jc2409/SF4_Data_Logger/schematics/LTSpice/audio_output_stage.asc

B1: bv; V=if(V(AUDIO) > V(TIMER), 5, 0)
C1: cap; 15n
C2: cap; 15n
C3: cap; 10u
R1: res; 2.2k
R2: res; 2.2k
R3: res; 220
U1: opamp2; LMX58_LM2904
U2: opamp2; LMX58_LM2904
V1: voltage; 5
V2: voltage; SINE(1.5 1.0 400)
V3: voltage; PULSE(0 5 0 8u 8u 1p 16u)
Named nets: 0, AUDIO, TIMER
.tran 50m
.lib snom268c/lmx58_lm2904.lib
.ic V(n003)=2.5 V(n002)=2.5
