jc2409/SF4_Data_Logger/schematics/LTSpice/full_circuit.asc

C1: cap; 10µ
C2: cap; 10µ
C3: cap; 10µ
C4: cap; 2.2n
C5: cap; 2.2n
C6: cap; 4.7µ
R1: res; 10k
R2: res; 10k
R3: res; 1Meg
R4: res; 10k
R5: res; 100k
R6: res; {R_LDR}
R7: res; 10k
R8: res; 10k
R9: res; 15k
R10: res; 15k
R11: res; 1Meg
U1: opamp2; TL072
U2: LTC6078
U3: opamp2; TL072
U4: LTC6078
U5: opamp2; LMX58_LM2904
V1: voltage; 5
V2: voltage; SINE(0 0.1 400); AC 1
Named nets: 0
.tran 10m
.inc sloj067/TL072.301
.step param R_LDR 100 100k 20k
.lib snom268c/lmx58_lm2904.lib
