jc2409/SF4_Data_Logger/schematics/LTSpice/output_stage.asc

B1: bv; V=if(V(AUDIO) > V(TIMER), 5, 0)
C1: cap; 33n
C2: cap; 10µ
R1: res; 1k
R2: res; 100k
U1: opamp2; LMX58_LM2904
V1: voltage; 5
V2: voltage; SINE(1.75 1.5 400)
V3: voltage; PULSE(0 5 0 8u 8u 1p 16u)
Named nets: 0, AUDIO, TIMER
.tran 10m startup
.lib snom268c/lmx58_lm2904.lib
