jc2409/SF4_Data_Logger/schematics/KiCad/SF4.kicad_sch

## KiCad design schematics/KiCad/SF4.kicad_sch (2026-06-06)

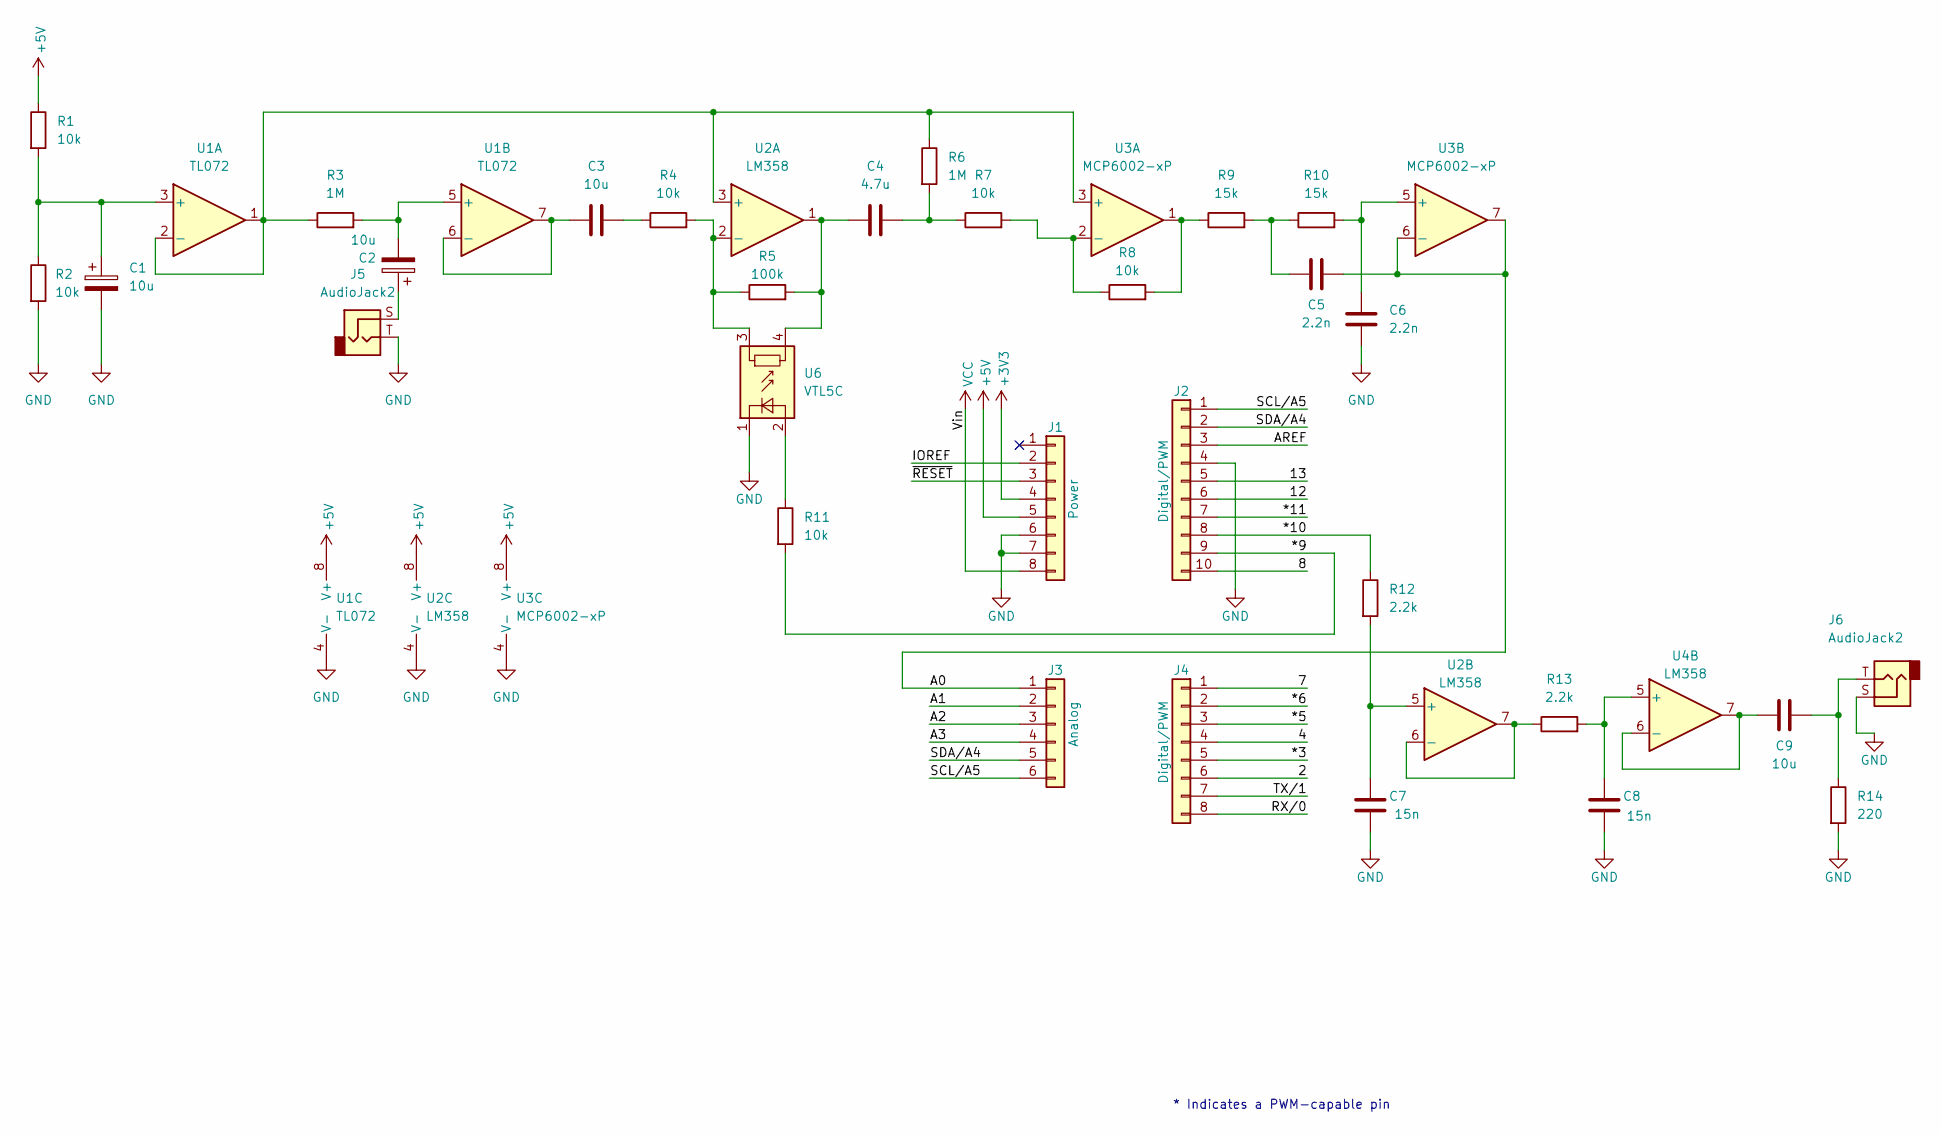
[picture p18: schematic SF4.kicad_sch]

Parts:
C1, C2, C3, C9: 10u
C4: 4.7u
C5, C6: 2.2n
C7, C8: 15n
J1: Power; PinSocket_1x08_P2.54mm_Vertical
J2: Digital/PWM; PinSocket_1x10_P2.54mm_Vertical
J3: Analog; PinSocket_1x06_P2.54mm_Vertical
J4: Digital/PWM; PinSocket_1x08_P2.54mm_Vertical
J5, J6: AudioJack2
R1, R2, R4, R7, R8, R11: 10k
R3, R6: 1M
R5: 100k
R9, R10: 15k
R12, R13: 2.2k
R14: 220
U1: TL072
U2, U4: LM358
U3: MCP6002-xP
U6: VTL5C; PerkinElmer_VTL5C

Connections:
2: J4.6
3: J4.5
4: J4.4
5: J4.3
6: J4.2
7: J4.1
8: J2.10
9: J2.9, R11.2
10: J2.8, R12.1
11: J2.7
12: J2.6
13: J2.5
+3V3: J1.4
+5V: J1.5, R1.1, U1.8 (V+), U2.8 (V+), U3.8 (V+)
A0: C5.2, J3.1, U3.6 (-), U3.7
A1: J3.2
A2: J3.3
A3: J3.4
AREF: J2.3
GND: C1.2, C6.2, C7.2, C8.2, J1.6, J1.7, J2.4, J5.T, J6.S, R2.2, R14.2, U1.4 (V-), U2.4 (V-), U3.4 (V-), U6.1 (-)
IOREF: J1.2
unnamed: C1.1, R1.2, R2.1, U1.3 (+)
unnamed: C2.1, J5.S
unnamed: C2.2, R3.2, U1.5 (+)
unnamed: C3.1, U1.6 (-), U1.7
unnamed: C3.2, R4.1
unnamed: C4.1, R5.2, U2.1, U6.4
unnamed: C4.2, R6.2, R7.1
unnamed: C5.1, R9.2, R10.1
unnamed: C6.1, R10.2, U3.5 (+)
unnamed: C7.1, R12.2, U2.5 (+)
unnamed: C8.1, R13.2, U4.5 (+)
unnamed: C9.1, U4.6 (-), U4.7
unnamed: C9.2, J6.T, R14.1
unnamed: R3.1, R6.1, U1.1, U1.2 (-), U2.3 (+), U3.3 (+)
unnamed: R4.2, R5.1, U2.2 (-), U6.3
unnamed: R7.2, R8.1, U3.2 (-)
unnamed: R8.2, R9.1, U3.1
unnamed: R11.1, U6.2 (+)
unnamed: R13.1, U2.6 (-), U2.7
RX/0: J4.8
SCL/A5: J2.1, J3.6
SDA/A4: J2.2, J3.5
TX/1: J4.7
VCC: J1.8
~RESET: J1.3

Notes on the sheet:
* Indicates a PWM-capable pin
